dekuNukem/duckyPad-expansion-modules/pcb/8ch/dimension drawings/dimensions.png

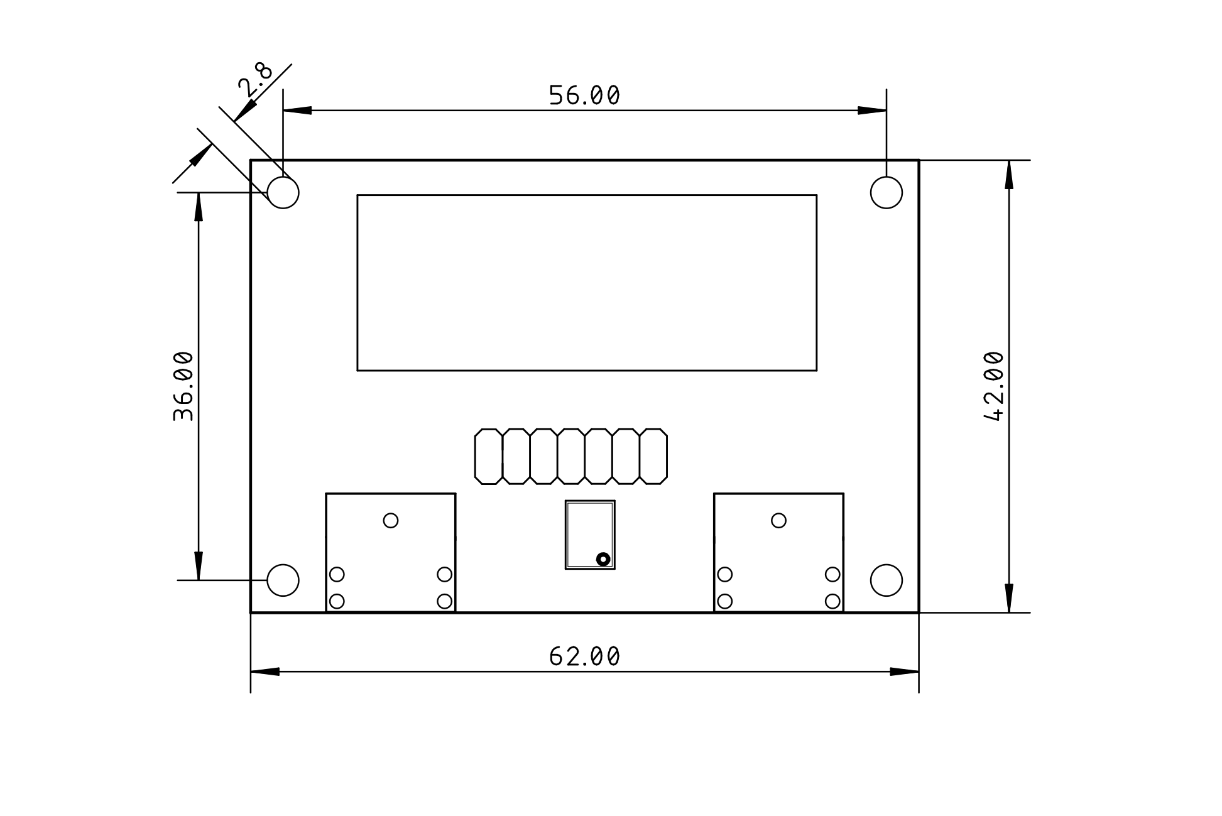
pcb/8ch/dimension drawings/dimensions.png
